PawprintPrototyping/arm-game/target_controller/PPPRobotTargetTransceiver/PPPRobotTargetTransceiver.kicad_sch

## KiCad design target_controller/PPPRobotTargetTransceiver/PPPRobotTargetTransceiver.kicad_sch (2024-06-12)

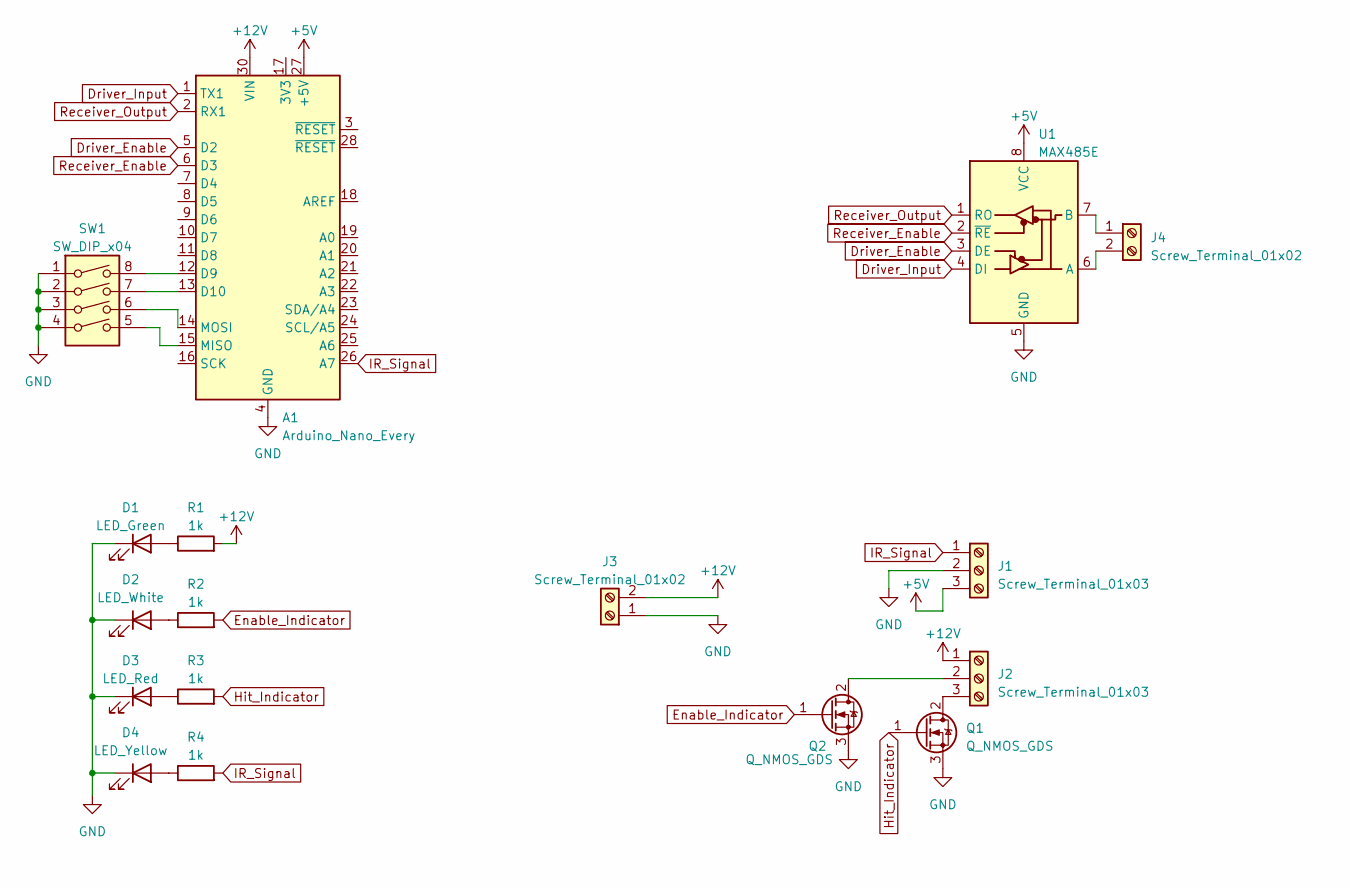
[picture p12: schematic PPPRobotTargetTransceiver.kicad_sch]

Parts:
A1: Arduino_Nano_Every; Arduino_Nano
D1: LED_Green
D2: LED_White
D3: LED_Red
D4: LED_Yellow
J1, J2: Screw_Terminal_01x03
J3, J4: Screw_Terminal_01x02
Q1, Q2: Q_NMOS_GDS
R1, R2, R3, R4: 1k
SW1: SW_DIP_x04
U1: MAX485E

Connections:
Driver_Enable: A1.5 (D2), U1.3 (DE)
Driver_Input: A1.1 (TX1), U1.4 (DI)
Enable_Indicator: Q2.1 (G), R2.2
Hit_Indicator: Q1.1 (G), R3.2
IR_Signal: A1.26 (A7), J1.1, R4.2
unnamed: A1.12 (D9), SW1.8
unnamed: A1.13 (D10), SW1.7
unnamed: A1.14 (MOSI), SW1.6
unnamed: A1.15 (MISO), SW1.5
unnamed: A1.4 (GND), A1.29 (GND)
unnamed: D1.1 (K), D2.1 (K), D3.1 (K), D4.1 (K)
unnamed: D1.2 (A), R1.1
unnamed: D2.2 (A), R2.1
unnamed: D3.2 (A), R3.1
unnamed: D4.2 (A), R4.1
unnamed: J2.2, Q2.2 (D)
unnamed: J2.3, Q1.2 (D)
unnamed: J4.1, U1.7 (B)
unnamed: J4.2, U1.6 (A)
unnamed: SW1.1, SW1.2, SW1.3, SW1.4
Receiver_Enable: A1.6 (D3), U1.2 (~RE)
Receiver_Output: A1.2 (RX1), U1.1 (RO)
