PawprintPrototyping/arm-game/sysio_stack_light/PPPRoboSysIOStackLight.kicad_sch

## KiCad design sysio_stack_light/PPPRoboSysIOStackLight.kicad_sch (2023-06-10)

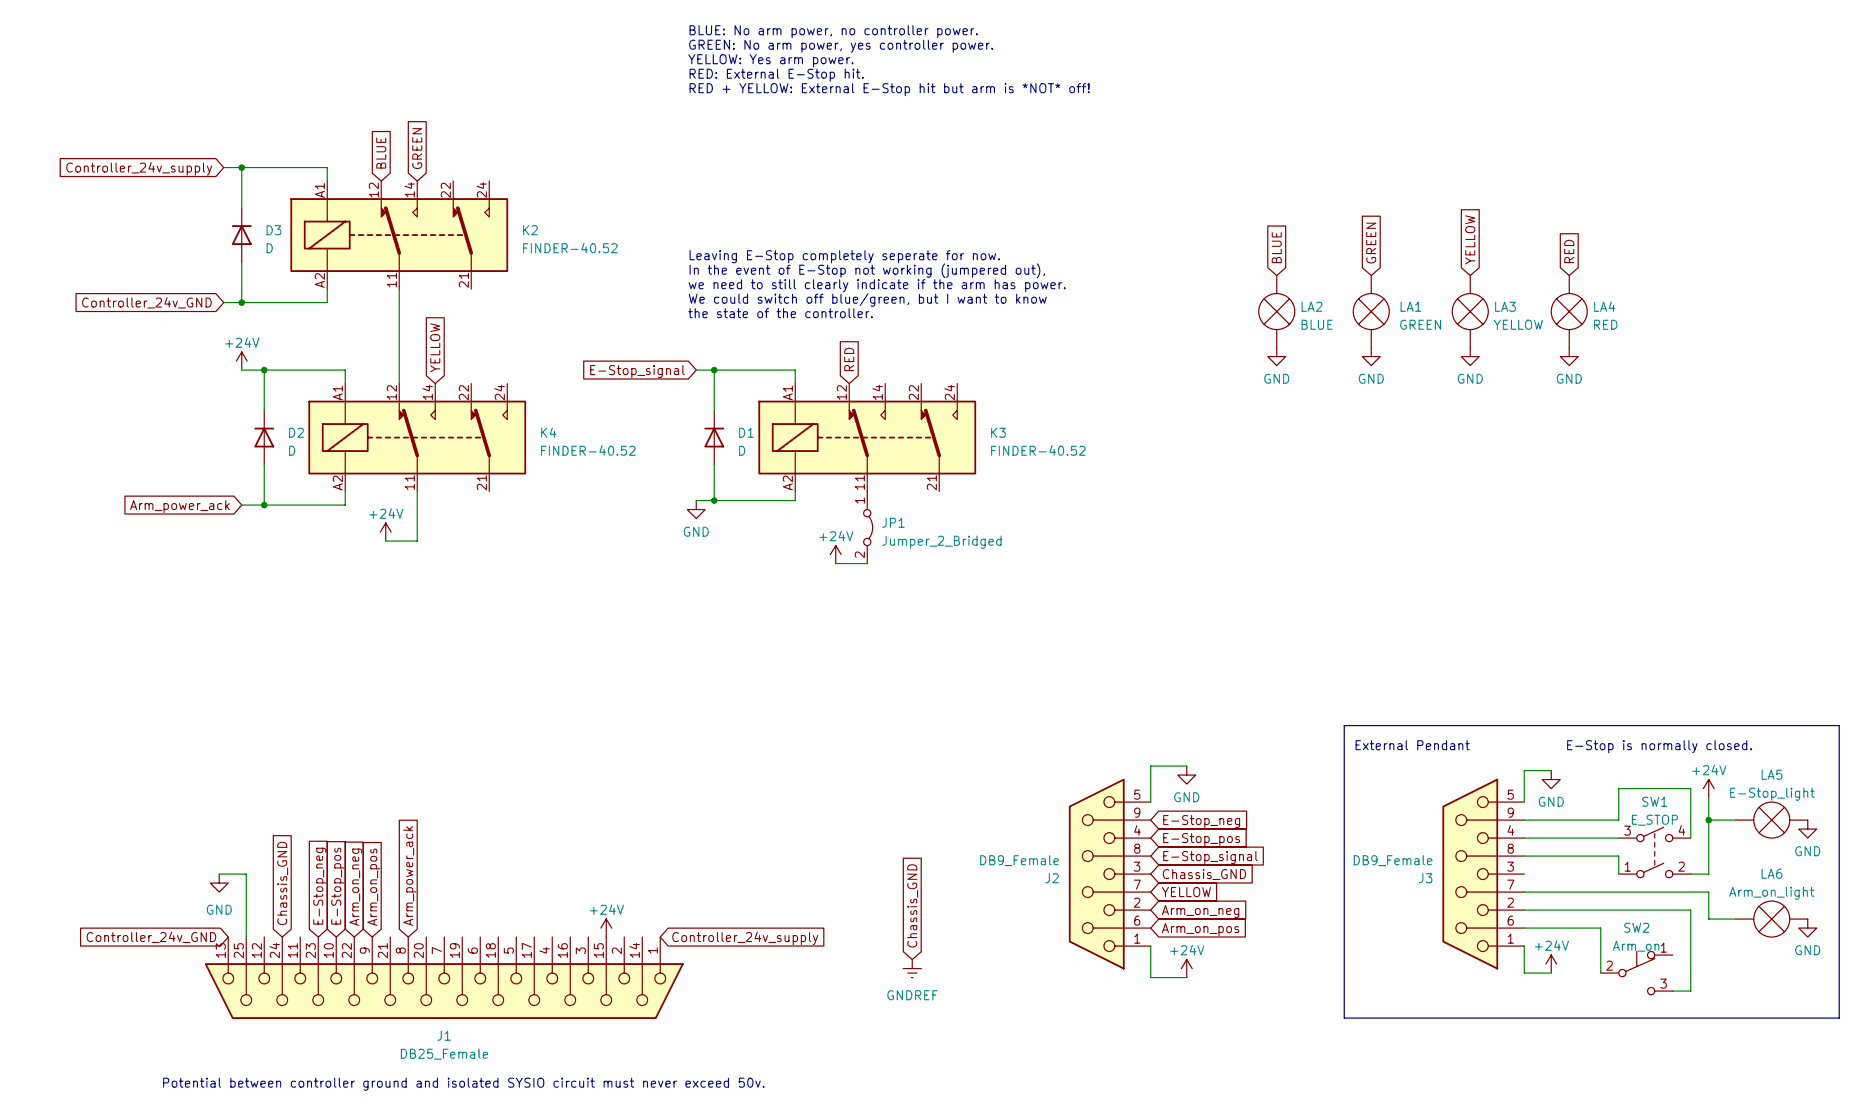
[picture p13: schematic PPPRoboSysIOStackLight.kicad_sch]

Parts:
D1, D2, D3: D
J1: DB25_Female
J2, J3: DB9_Female
JP1: Jumper_2_Bridged
K2, K3, K4: FINDER-40.52; Relay_DPDT_Finder_40.52
LA1: GREEN
LA2: BLUE
LA3: YELLOW
LA4: RED
LA5: E-Stop_light
LA6: Arm_on_light
SW1: E_STOP
SW2: Arm_on

Connections:
Arm_on_neg: J1.22, J2.2
Arm_on_pos: J1.9, J2.6
Arm_power_ack: D2.2 (A), J1.8, K4.A2
BLUE: K2.12, LA2.2 (+)
Chassis_GND: J1.24, J2.3
Controller_24v_GND: D3.2 (A), J1.13, K2.A2
Controller_24v_supply: D3.1 (K), J1.1, K2.A1
E-Stop_neg: J1.23, J2.9
E-Stop_pos: J1.10, J2.4
E-Stop_signal: D1.1 (K), J2.8, K3.A1
GREEN: K2.14, LA1.2 (+)
unnamed: D1.2 (A), K3.A2
unnamed: D2.1 (K), K4.A1
unnamed: J3.2, SW2.3 (C)
unnamed: J3.4, SW1.3
unnamed: J3.6, SW2.2 (B)
unnamed: J3.7, LA6.2 (+)
unnamed: J3.8, SW1.1
unnamed: J3.9, SW1.4
unnamed: JP1.1 (A), K3.11
unnamed: K2.11, K4.12
unnamed: LA5.2 (+), SW1.2
RED: K3.12, LA4.2 (+)
YELLOW: J2.7, K4.14, LA3.2 (+)

Notes on the sheet:
Leaving E-Stop completely seperate for now. In the event of E-Stop not working (jumpered out), we need to still clearly indicate if the arm has power. We could switch off blue/green, but I want to know the state of the controller.
BLUE: No arm power, no controller power. GREEN: No arm power, yes controller power. YELLOW: Yes arm power. RED: External E-Stop hit. RED + YELLOW: External E-Stop hit but arm is *NOT* off!
Potential between controller ground and isolated SYSIO circuit must never exceed 50v.
External Pendant
E-Stop is normally closed.
