PawprintPrototyping/arm-game/scoreboard/scoreboard.py

#!/usr/bin/env python
import json
import os
import threading
import logging
import structlog
import time
import random

from paho.mqtt import publish as mqtt
from rgbbase import RGBBase

DEBUG = os.getenv("DEBUG", "False").lower() in ("true", "1", "t")
MQTT_HOSTNAME = os.getenv("MQTT_HOSTNAME", "localhost")

if DEBUG:
    from RGBMatrixEmulator import graphics
else:
    from rgbmatrix import graphics



DEBUG = os.getenv("DEBUG", "False").lower() in ("true", "1", "t")

if DEBUG:
    logging.basicConfig(level=logging.DEBUG)
logging.basicConfig(level=logging.DEBUG)
log = structlog.getLogger(__name__)

class Scoreboard(RGBBase):
    IDLE = "idle"
    CLEAR = "clear"
    TIMER = "timer"
    GAME_OVER = "game_over"

    def __init__(self, *args, **kwargs):
        super(Scoreboard, self).__init__(*args, **kwargs)

        self.state = Scoreboard.IDLE
        self.message_data = {}
        self.minutes = kwargs.get("minutes", 1)
        self.seconds = kwargs.get("seconds", 0)
        self.stop = False
        self.pause = False
        self.delay_thread = threading.Thread()

        self.black = graphics.Color(0, 0, 0)
        self.big_font = graphics.Font()
        self.big_font.LoadFont("fonts/texgyre-27.bdf")

        self.font = graphics.Font()
        self.font.LoadFont("fonts/10x20.bdf")

        self.small_font = graphics.Font()
        self.small_font.LoadFont("fonts/5x8.bdf")

    def run(self):
        log.debug("Scoreboard thread running")
        while not self.stop:
            match self.state:
                case Scoreboard.TIMER:
                    self.timer()
                case Scoreboard.GAME_OVER:
                    self.game_over()
                    self.state = Scoreboard.IDLE
                case Scoreboard.CLEAR:
                    self.clear()
                    self.state = Scoreboard.IDLE
            time.sleep(0.1)

    def timer(self, timer_minutes=None, timer_seconds=None):
        if timer_minutes is None:
            timer_minutes = self.minutes
        if timer_seconds is None:
            timer_seconds = self.seconds
        canvas = self.matrix.CreateFrameCanvas()

        red = graphics.Color(255, 0, 0)
        yellow = graphics.Color(255, 255, 0)
        green = graphics.Color(0, 255, 0)
        blue = graphics.Color(0, 0, 255)
        white = graphics.Color(255, 255, 255)

        message_colors = [yellow, green, blue, white]
        encouraging_message = self.get_encouraging_message()
        encouraging_color = random.choice(message_colors)

        #graphics.DrawLine(canvas, 5, 5, 22, 13, red)
        for minutes in range(timer_minutes, -1, -1):
            # FIXME: Can't actually set seconds here
            for seconds in range(timer_seconds, -1, -1):
                if seconds % 7 == 0:
                    encouraging_message = self.get_encouraging_message()
                    encouraging_color = random.choice(message_colors)
                for dsec in range(9, -1, -1):
                    canvas.Clear()
                    sep = ":"
                    if dsec % 2:
                        sep = " "
                    color = yellow
                    if minutes == 0 and seconds < 30:
                        color = red

                    graphics.DrawText(canvas, self.font, 1, 25, color, f"{minutes:>2}:{seconds:>02}{'.' if sep == ':' else ' '}{dsec}")
                    graphics.DrawText(canvas, self.small_font, 75, 22, encouraging_color, encouraging_message)

                    canvas = self.matrix.SwapOnVSync(canvas)
                    time.sleep(0.1)
                    if self.state != Scoreboard.TIMER:
                        return

            timer_seconds = 59

        self.state = Scoreboard.GAME_OVER

        #graphics.DrawCircle(canvas, 15, 15, 10, green)

    def game_over(self, blocking=False):
        canvas = self.matrix.CreateFrameCanvas()
        canvas.Clear()
        canvas.Fill(255, 0, 0)
        message = self.message_data.get("text", "GAME OVER")
        x = self.message_data.get("x", 12)
        y = self.message_data.get("y", 25)
        graphics.DrawText(canvas, self.big_font, x, y, self.black, message)
        self.matrix.SwapOnVSync(canvas)
        mqtt.single(f"scoreboard/timer/game_over", "GAME OVER", hostname=MQTT_HOSTNAME)

    def clear(self):
        canvas = self.matrix.CreateFrameCanvas()
        canvas.Clear()
        self.matrix.SwapOnVSync(canvas)

    def get_encouraging_message(self):
        potential_messages = [
          "You're doing good!",
          "Shoot that robot!",
          "Seeya, space cowboy",
          "[Encouraging Message 4]",
          "Sharp shootin', Tex",
          "Bang!",
          "You got me!",
          "*dabs*",
          "Now you're lasering!",
          "Bite my shiny robot ass",
          "Do a barrel roll!",
        ]
        return random.choice(potential_messages)


# Main function
if __name__ == "__main__":
    graphics_test = Scoreboard()
    if (not graphics_test.process()):
        graphics_test.print_help()
