PawprintPrototyping/arm-game/motion/target_blinkies.py

import json
import os
import threading
import time
import random

import structlog
from paho.mqtt import publish as mqtt

from target_scoring_serial import TargetScoringSerial

CHANCE_DOUBLE_SCORE = 0.2
MINIMUM_SLEEP_TIME = 0.1

logger = structlog.get_logger()
MQTT_HOST = os.getenv("MQTT_HOST", "localhost")
DEBUG = os.getenv("DEBUG", "False").lower() in ("true", "1", "t")

class TargetBlinkies(object):
    def __init__(self,  mqtt_host=MQTT_HOST):
        self.mqtt_host = mqtt_host
        self.stop = False
        self.thread = threading.Thread(target=self.run)
        self.enabled = False
        # Populated from the retained `targets/available` topic published by target_scoring_serial
        self.target_ids = list(TargetScoringSerial.TARGET_IDS)

    def update_target_ids(self, payload):
        if isinstance(payload, (bytes, str)):
            try:
                data = json.loads(payload)
            except (ValueError, TypeError) as e:
                logger.warn("Ignoring malformed targets/available payload", payload=payload, error=str(e))
                return
        else:
            data = payload

        if isinstance(data, dict):
            data = data.get("targets", [])
        if not isinstance(data, list):
            logger.warn("Ignoring targets/available payload with unexpected shape",
                        payload=payload)
            return

        try:
            new_ids = [int(t) for t in data]
        except (TypeError, ValueError) as exc:
            logger.warn("Ignoring targets/available payload with non-integer IDs", payload=payload, error=str(exc))
            return

        if new_ids != self.target_ids:
            logger.info("Updated live target list", old=self.target_ids, new=new_ids)
            self.target_ids = new_ids # Atomic replace

    def publish_enable(self, target_id):
        logger.info("Enable target", target_id=target_id, actuion="enable")
        mqtt.single(f"targets/{target_id}/enable", f"enable {target_id}", hostname=self.mqtt_host)

    def publish_disable(self, target_id):
        #if self.enabled:
        logger.info("Disable target", target_id=target_id, action="disable")
        mqtt.single(f"targets/{target_id}/disable", f"disable {target_id}", hostname=self.mqtt_host)

    def publish_up(self, target_id):
        logger.info("Move target up", target_id=target_id, action="up")
        mqtt.single(f"targets/{target_id}/up", f"up {target_id}", hostname=self.mqtt_host)

    def publish_down(self, target_id):
        logger.info("Move target down", target_id=target_id, action="down")
        mqtt.single(f"targets/{target_id}/down", f"down {target_id}", hostname=self.mqtt_host)

    def publish_home(self, target_id):
        logger.info("Home target", target_id=target_id, action="home")
        mqtt.single(f"targets/{target_id}/home", f"home {target_id}", hostname=self.mqtt_host)

    def game_start(self):
        logger.info("Home all targets")
        for target in list(self.target_ids):
            self.publish_home(target)

    def game_over(self):
        logger.info("Disable all targets")
        for target in list(self.target_ids):
            self.publish_disable(target)
            self.publish_home(target)

    def run(self):
        while not self.stop:
            if self.enabled:
                # Copy the list so a mid-iteration update doesn't cause us to pick a target we've already hidden.
                target_list = list(self.target_ids)
                if not target_list:
                    # Nothing discovered yet
                    time.sleep(MINIMUM_SLEEP_TIME)
                    continue
                # Sleep some random amount of time
                off_time = random.random() + MINIMUM_SLEEP_TIME
                time.sleep(off_time)


                # Select 2 to 4 Random Targets
                targets_to_show_count = min(random.randint(2,4), len(target_list))
                show_targets = random.sample(target_list, targets_to_show_count)
                for t in show_targets:
                    if not self.enabled:
                        break
                    self.publish_up(t)
                time.sleep(random.uniform(0.5, 1.5))

                # Enable subset of chosen targets
                targets_to_enable_count = random.randint(min(2, len(target_list)), targets_to_show_count)
                enable_targets = random.sample(show_targets, targets_to_enable_count)

                for t in enable_targets:
                    if not self.enabled:
                        break
                    self.publish_enable(t)

                # Dwell for a time
                on_time = random.uniform(0.5, 1.5)
                time.sleep(on_time)

                # Turn off the target(s)
                for t in enable_targets:
                    self.publish_disable(t)
                    time.sleep(random.uniform(0.1, 0.4))

                # Hide the targets
                for t in show_targets:
                    self.publish_down(t)

            else:
                time.sleep(MINIMUM_SLEEP_TIME)


if __name__ == "__main__":
    blinkies = TargetBlinkies()
    blinkies.run()
